rabs664/Amstrad-CPC-IO-Logger/VSCode/CPC_IO_Logger/GPIOPins.h

/* GPIO Pins for CPC IO Logger */

#include "hardware/pio.h"

#define P_A0 0
#define P_A1 1
#define P_A8 2
#define P_A9 3
#define P_A10 4
#define P_A11 5
#define P_A12 6
#define P_A13 7
#define P_A14 8
#define P_A15 9
#define P_D0 10
#define P_D1 11
#define P_D2 12
#define P_D3 13
#define P_D4 14
#define P_D5 15
#define P_D6 16
#define P_D7 17
#define P_DBGC 18

#define P_IOWR 27
#define P_CSRD 26
#define P_DATA_AB 22
#define P_DATA_CE 21
#define P_ADHB_CE 20
#define P_CTRL_CE 19


void setup_gpio_pins(PIO pio);
